Cuprum77/BananaBoard/Images/575-4.webp

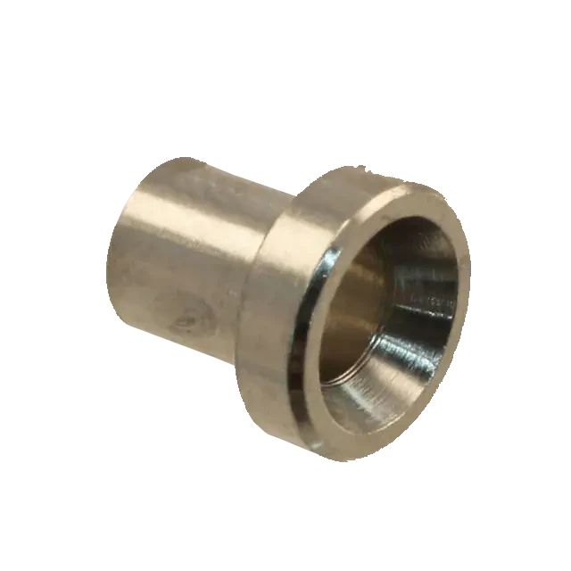
Images/575-4.webp
